TehoorMarjan/HalloweenSkull/mechanical/IMG_20251029_183111.jpg

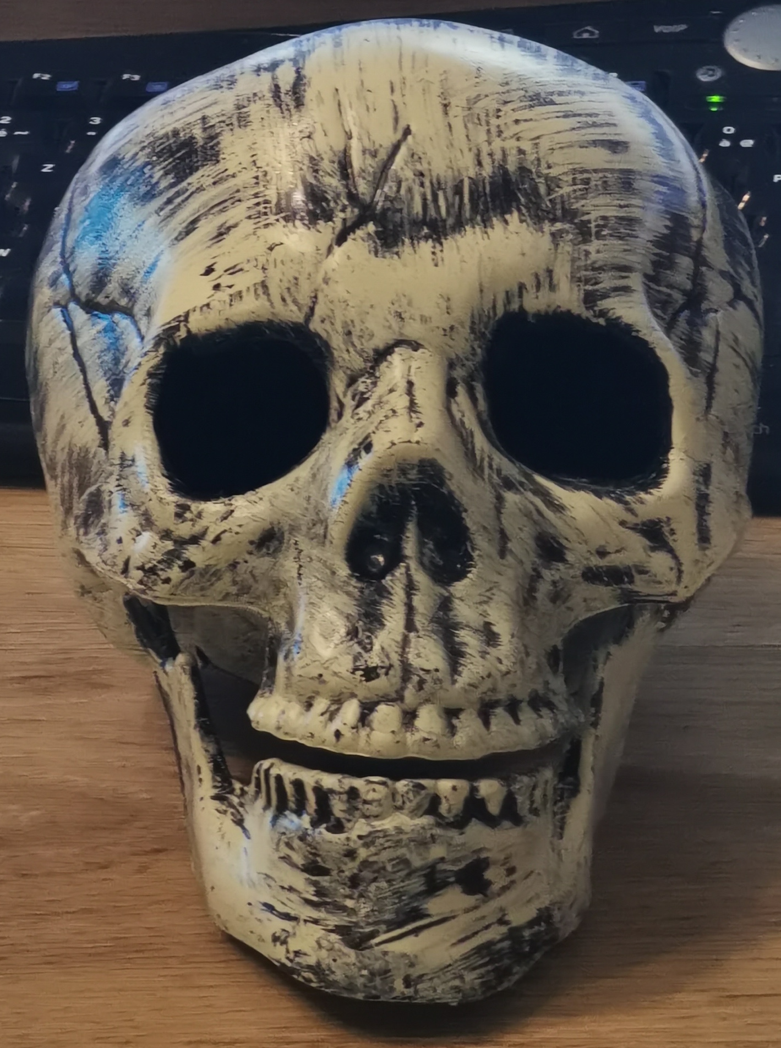
mechanical/IMG_20251029_183111.jpg
