TehoorMarjan/HalloweenSkull/mechanical/IMG_20251029_183227.jpg

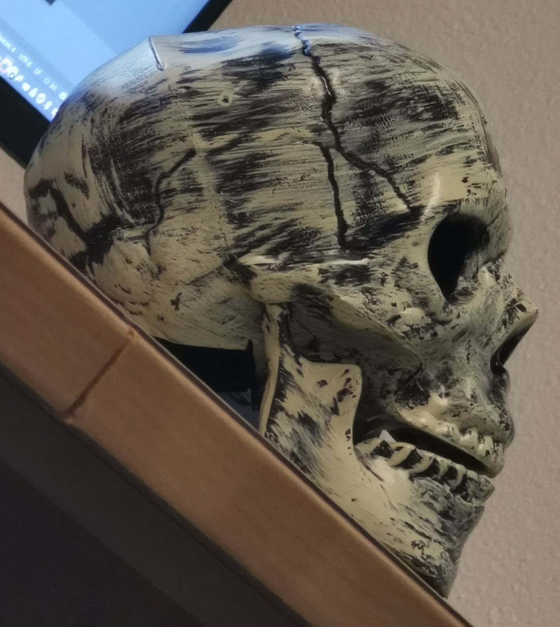
mechanical/IMG_20251029_183227.jpg
